Aronnax9000/Vega816/kicad/Vega816/VectorPullRewrite/VectorPullRewrite.kicad_pcb

## KiCad design ecad/ecad.kicad_sch

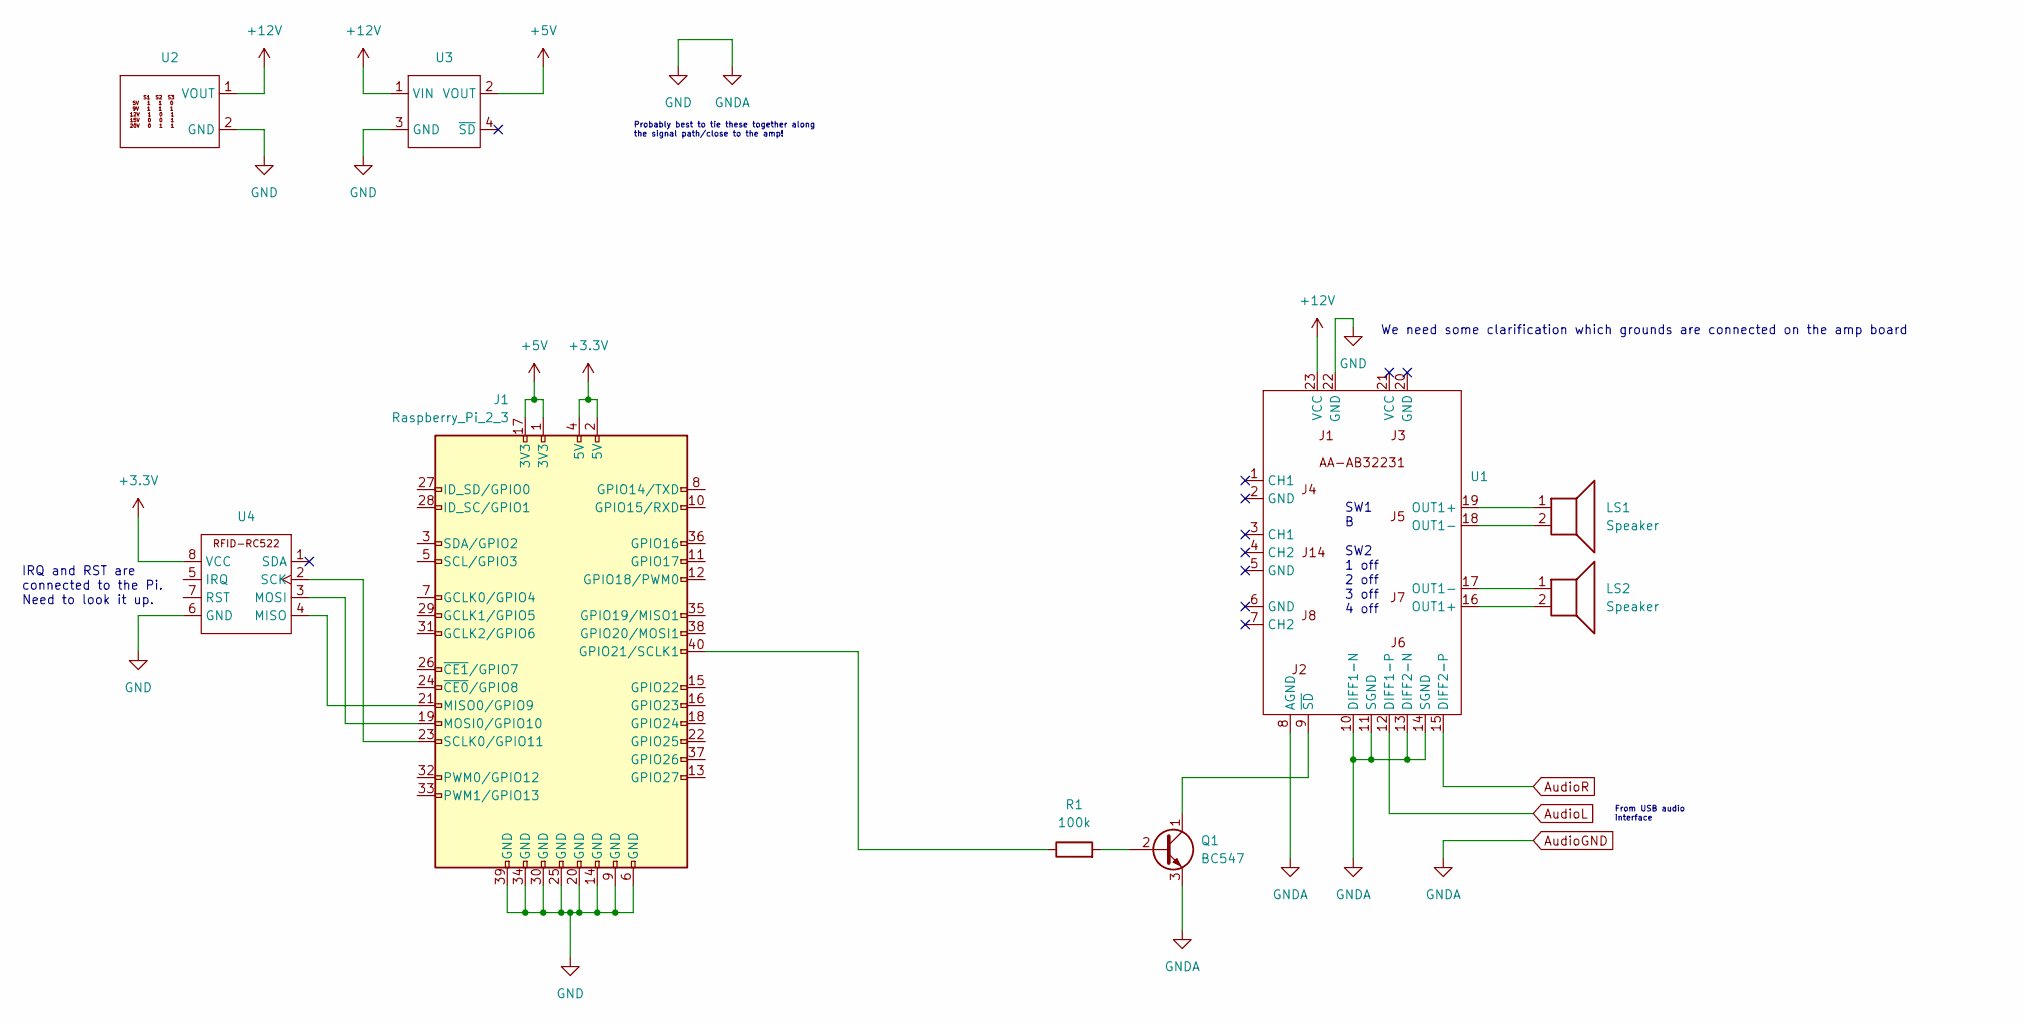
[picture p6: schematic ecad.kicad_sch]

Parts:
J1: Raspberry_Pi_2_3
LS1, LS2: Speaker
Q1: BC547; TO-92_Inline
R1: 100k
U1, U2, U3, U4: (no value)

Connections:
+3.3V: J1.2 (5V), J1.4 (5V), U4.8 (VCC)
+5V: J1.1 (3V3), J1.17 (3V3), U3.2 (VOUT)
+12V: U1.23 (VCC), U2.1 (VOUT), U3.1 (VIN)
AudioGND: J1.6 (GND), J1.9 (GND), J1.14 (GND), J1.20 (GND), J1.25 (GND), J1.30 (GND), J1.34 (GND), J1.39 (GND), Q1.3 (E), U1.8 (AGND), U1.10 (DIFF1-N), U1.11 (SGND), U1.13 (DIFF2-N), U1.14 (SGND), U1.22 (GND), U2.2 (GND), U3.3 (GND), U4.6 (GND)
AudioL: U1.12 (DIFF1-P)
AudioR: U1.15 (DIFF2-P)
unnamed: J1.19 (MOSI0/GPIO10), U4.3 (MOSI)
unnamed: J1.21 (MISO0/GPIO9), U4.4 (MISO)
unnamed: J1.23 (SCLK0/GPIO11), U4.2 (SCK)
unnamed: J1.40 (GPIO21/SCLK1), R1.1
unnamed: LS1.1, U1.19 (OUT1+)
unnamed: LS1.2, U1.18 (OUT1-)
unnamed: LS2.1, U1.17 (OUT1-)
unnamed: LS2.2, U1.16 (OUT1+)
unnamed: Q1.1 (C), U1.9 (~SD)
unnamed: Q1.2 (B), R1.2

Notes on the sheet:
IRQ and RST are connected to the Pi. Need to look it up.
Probably best to tie these together along the signal path/close to the amp!
From USB audio interface
We need some clarification which grounds are connected on the amp board
SW1 B SW2 1 off 2 off 3 off 4 off
